ehajo/SenseHaJo/Original/display-bilder/mengenstufe-1.png

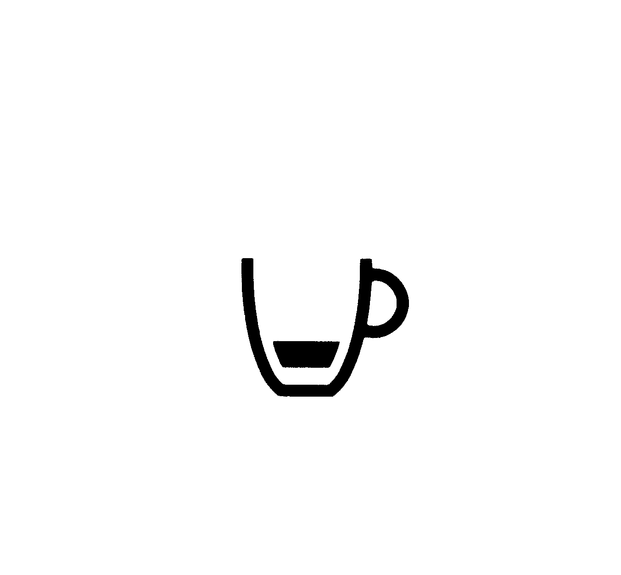
Original/display-bilder/mengenstufe-1.png
