ehajo/SenseHaJo/Original/display-bilder/mengenstufe-2.png

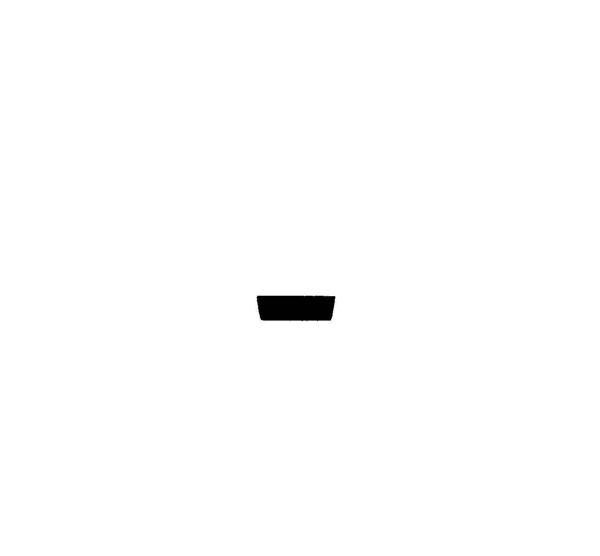
Original/display-bilder/mengenstufe-2.png
