ehajo/SenseHaJo/Original/display-bilder/mengenwahl.png

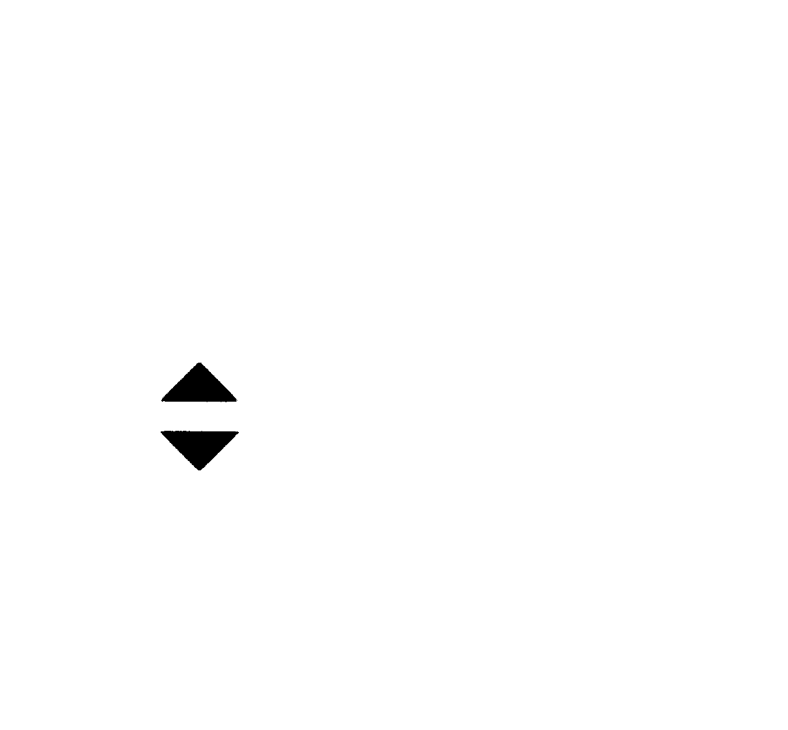
Original/display-bilder/mengenwahl.png
