ehajo/SenseHaJo/Original/display-protocol.PNG

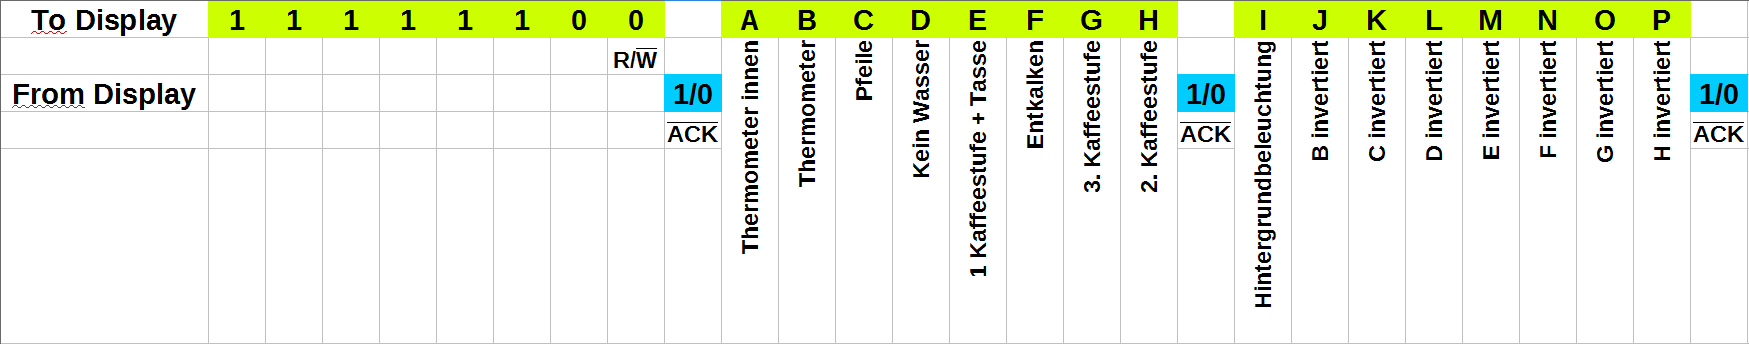
Original/display-protocol.PNG
