ehajo/SenseHaJo/Original/display-taste-1.PNG

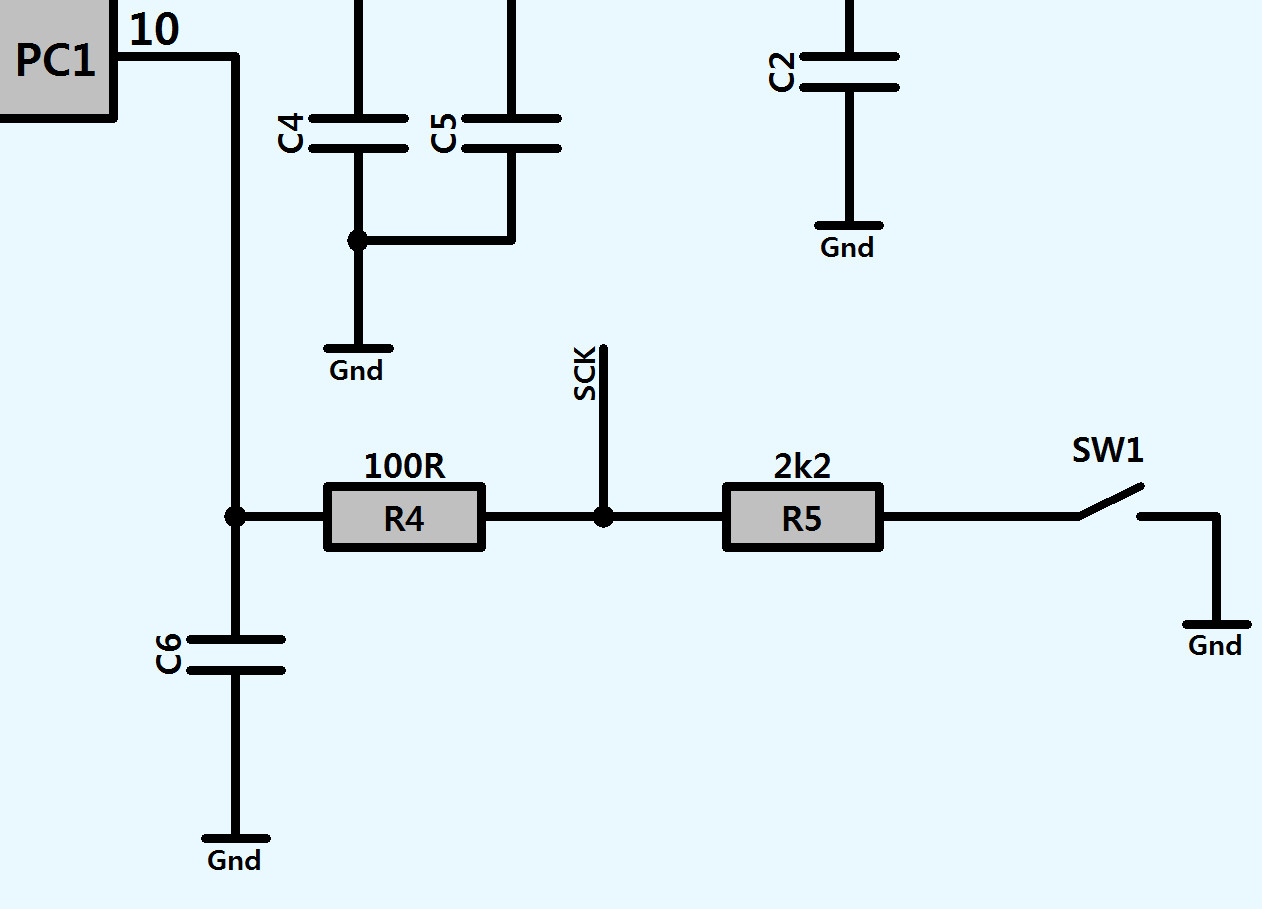
Original/display-taste-1.PNG
