ehajo/SenseHaJo/Original/netzteil.PNG

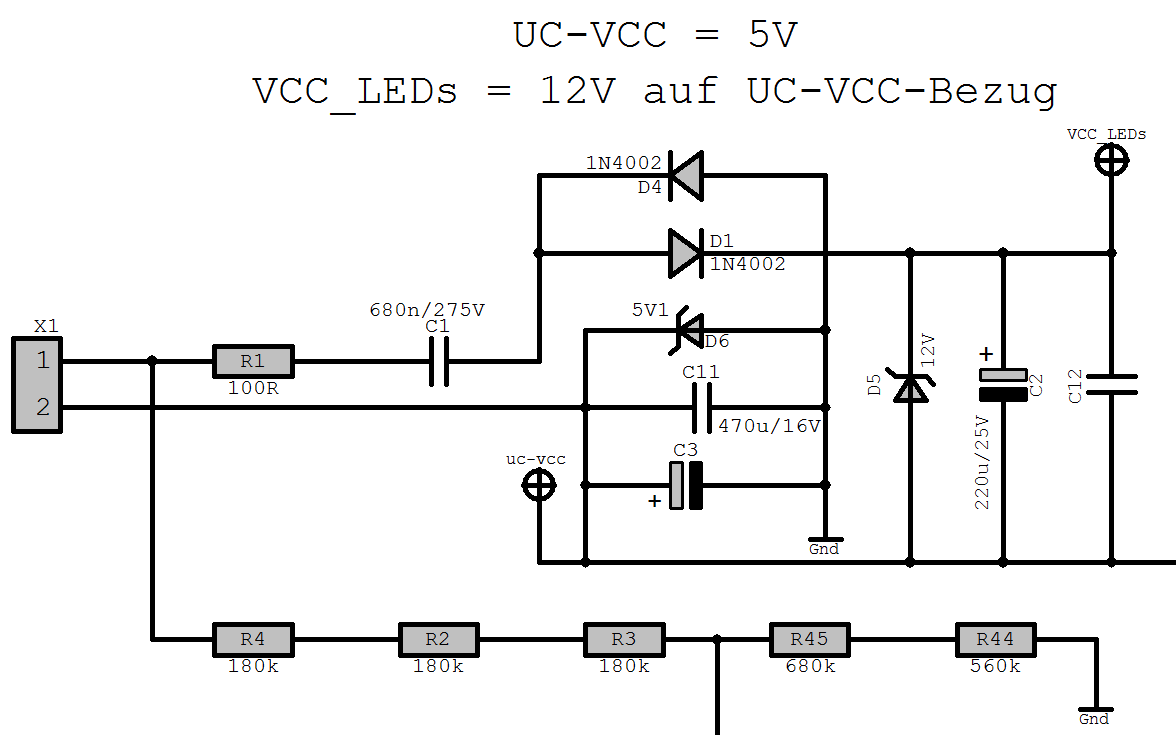
Original/netzteil.PNG
