ehajo/SenseHaJo/Original/nulldurchgang.png

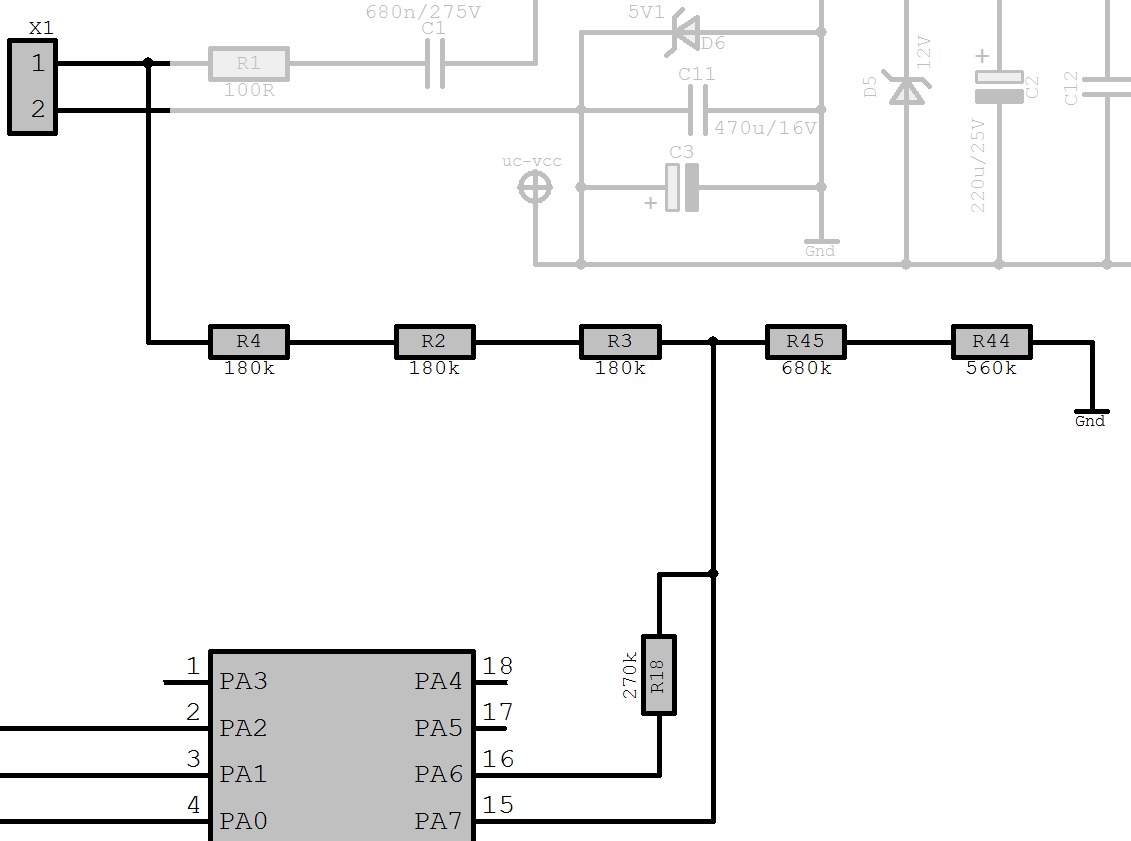
Original/nulldurchgang.png
