ehajo/SenseHaJo/Original/Simulation/Spannungen.png

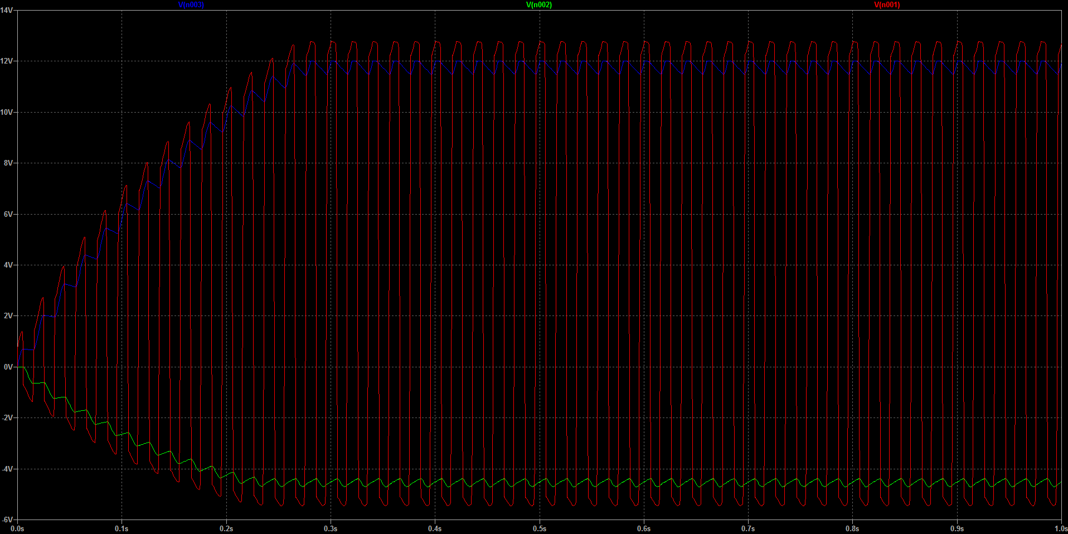
Original/Simulation/Spannungen.png
