ehajo/SenseHaJo/Original/Simulation/Draft1.asc

C1: cap; 680n
C2: cap; 100n
C3: polcap; 470µ
C4: cap; 100n
C5: polcap; 220µ
D1: diode
D2: diode
D3: zener; 1N750
D4: zener; UDZV12B
R1: res; 100R
R2: res; 470R
R3: res; 1200R
V1: voltage; SINE(0 230 50)
Named nets: 0
.tran 1s
