ehajo/SenseHaJo/mkI/Software-mkI/Coffe_Maker_MKI/driver/Timer/Timer.h

/*
 * Timer.h
 *
 * Created: 31.12.2016 01:39:07
 *  Author: CalM
 */ 

  /*
  * www.eHaJo.de
  * All rights reserved
  * (C) 2016-2017
  */


#ifndef TIMER_H_
#define TIMER_H_

void voInit_HwTimer( void );
uint16_t u16GetSystemTicks();
uint16_t u16GetSystemTicksMS();


#endif /* TIMER_H_ */
