ehajo/SenseHaJo/mkI/Software-mkI/Coffe_Maker_MKI/driver/gpio/gpio_typedef.h

/*
 * gpio_typedef.h
 *
 * Created: 25.01.2017 23:05:58
 *  Author: calm
 */ 

  /*
  * www.eHaJo.de
  * All rights reserved
  * (C) 2016-2017
  */


#ifndef GPIO_TYPEDEF_H_
#define GPIO_TYPEDEF_H_

typedef enum { LED_ON , LED_OFF , LED_TOGGLE} emLEDSATATE;
typedef enum { SWITCH_PRESSED, SWITCH_RELEASED} emSWITCHSTATE;
typedef enum { POWER_ON, POWER_OFF} emPOWERSTATE;


#endif /* GPIO_TYPEDEF_H_ */
